Outdatedcandy92/Pedalboard/src/DS-1 V2/KiCad/Distortion-v2.kicad_sch

## KiCad design src/DS-1 V2/KiCad/Distortion-v2.kicad_sch (2025-06-08)

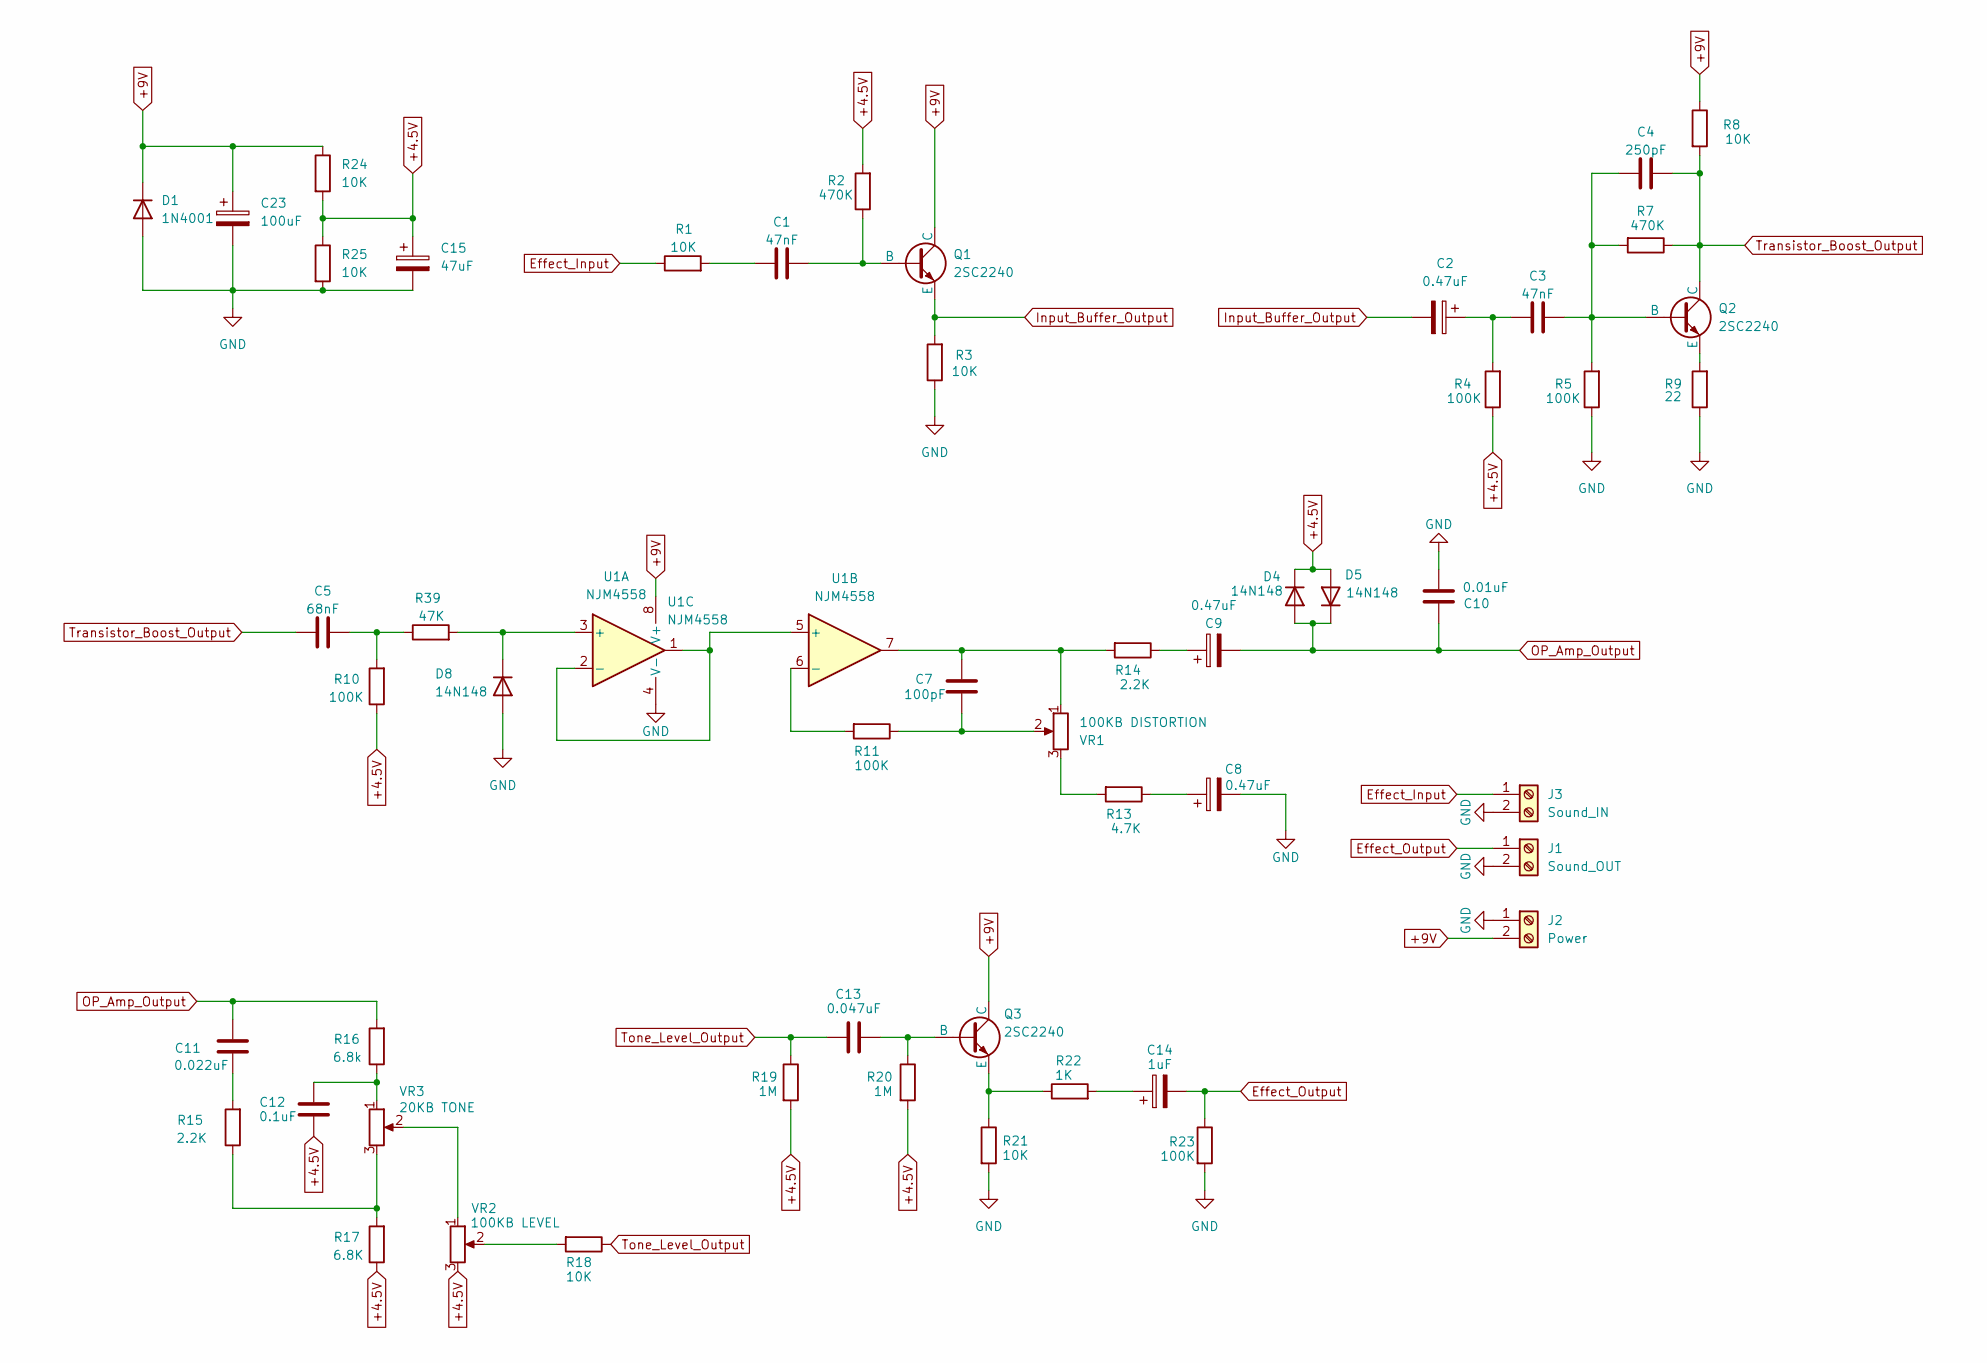
[picture p8: schematic Distortion-v2.kicad_sch]

Parts:
C1, C3: 47nF; C_Disc_D5.0mm_W2.5mm_P2.50mm
C2, C8, C9: 0.47uF; CP_Radial_D5.0mm_P2.50mm
C4: 250pF; C_Disc_D5.0mm_W2.5mm_P2.50mm
C5: 68nF; C_Disc_D5.0mm_W2.5mm_P2.50mm
C7: 100pF; C_Disc_D5.0mm_W2.5mm_P2.50mm
C10: 0.01uF; C_Disc_D5.0mm_W2.5mm_P2.50mm
C11: 0.022uF; C_Disc_D5.0mm_W2.5mm_P2.50mm
C12: 0.1uF; C_Disc_D5.0mm_W2.5mm_P2.50mm
C13: 0.047uF; C_Disc_D5.0mm_W2.5mm_P2.50mm
C14: 1uF; CP_Radial_D5.0mm_P2.50mm
C15: 47uF; CP_Radial_D5.0mm_P2.50mm
C23: 100uF; CP_Radial_D5.0mm_P2.50mm
D1: 1N4001; D_DO-35_SOD27_P7.62mm_Horizontal
D4, D5, D8: 14N148; D_DO-35_SOD27_P7.62mm_Horizontal
J1: Sound_OUT; TerminalBlock_Phoenix_MPT-0,5-2-2.54_1x02_P2.54mm_Horizontal
J2: Power; TerminalBlock_Phoenix_MPT-0,5-2-2.54_1x02_P2.54mm_Horizontal
J3: Sound_IN; TerminalBlock_Phoenix_MPT-0,5-2-2.54_1x02_P2.54mm_Horizontal
Q1, Q2, Q3: 2SC2240; TO-92L_Inline_Wide
R1, R3, R8, R18, R21, R24, R25: 10K; R_Axial_DIN0207_L6.3mm_D2.5mm_P10.16mm_Horizontal
R2, R7: 470K; R_Axial_DIN0207_L6.3mm_D2.5mm_P10.16mm_Horizontal
R4, R5, R10, R11, R23: 100K; R_Axial_DIN0207_L6.3mm_D2.5mm_P10.16mm_Horizontal
R9: 22; R_Axial_DIN0207_L6.3mm_D2.5mm_P10.16mm_Horizontal
R13: 4.7K; R_Axial_DIN0207_L6.3mm_D2.5mm_P10.16mm_Horizontal
R14, R15: 2.2K; R_Axial_DIN0207_L6.3mm_D2.5mm_P10.16mm_Horizontal
R16: 6.8k; R_Axial_DIN0207_L6.3mm_D2.5mm_P10.16mm_Horizontal
R17: 6.8K; R_Axial_DIN0207_L6.3mm_D2.5mm_P10.16mm_Horizontal
R19, R20: 1M; R_Axial_DIN0207_L6.3mm_D2.5mm_P10.16mm_Horizontal
R22: 1K; R_Axial_DIN0207_L6.3mm_D2.5mm_P10.16mm_Horizontal
R39: 47K; R_Axial_DIN0207_L6.3mm_D2.5mm_P10.16mm_Horizontal
U1: NJM4558; SIP-8_19x3mm_P2.54mm
VR1: 100KB DISTORTION; TerminalBlock_Phoenix_MPT-0,5-3-2.54_1x03_P2.54mm_Horizontal
VR2: 100KB LEVEL; TerminalBlock_Phoenix_MPT-0,5-3-2.54_1x03_P2.54mm_Horizontal
VR3: 20KB TONE; TerminalBlock_Phoenix_MPT-0,5-3-2.54_1x03_P2.54mm_Horizontal

Connections:
+4.5V: C12.1, C15.1, D4.1 (K), D5.2 (A), R2.2, R4.1, R10.1, R17.1, R19.2, R20.2, R24.2, R25.1, VR2.3
+9V: C23.1, D1.1 (K), J2.2, Q1.1 (C), Q3.1 (C), R8.1, R24.1, U1.8 (V+)
Effect_Input: J3.1, R1.1
Effect_Output: C14.2, J1.1, R23.1
GND: C8.2, C10.1, C15.2, C23.2, D1.2 (A), D8.2 (A), J1.2, J2.1, J3.2, R3.1, R5.1, R9.1, R21.2, R23.2, R25.2, U1.4 (V-)
Input_Buffer_Output: C2.2, Q1.3 (E), R3.2
unnamed: C1.1, R1.2
unnamed: C1.2, Q1.2 (B), R2.1
unnamed: C2.1, C3.1, R4.2
unnamed: C3.2, C4.1, Q2.2 (B), R5.2, R7.2
unnamed: C5.2, R10.2, R39.1
unnamed: C7.1, R11.1, VR1.2
unnamed: C7.2, R14.2, U1.7, VR1.1
unnamed: C8.1, R13.1
unnamed: C9.1, R14.1
unnamed: C11.1, R15.2
unnamed: C12.2, R16.1, VR3.1
unnamed: C13.1, Q3.2 (B), R20.1
unnamed: C14.1, R22.2
unnamed: D8.1 (K), R39.2, U1.3 (+)
unnamed: Q2.3 (E), R9.2
unnamed: Q3.3 (E), R21.1, R22.1
unnamed: R11.2, U1.6 (-)
unnamed: R13.2, VR1.3
unnamed: R15.1, R17.2, VR3.3
unnamed: R18.2, VR2.2
unnamed: U1.1, U1.2 (-), U1.5 (+)
unnamed: VR2.1, VR3.2
OP_Amp_Output: C9.2, C10.2, C11.2, D4.2 (A), D5.1 (K), R16.2
Tone_Level_Output: C13.2, R18.1, R19.1
Transistor_Boost_Output: C4.2, C5.1, Q2.1 (C), R7.1, R8.2
